harisovcina/Air/3Ddesign/3dprintedparts.jpg

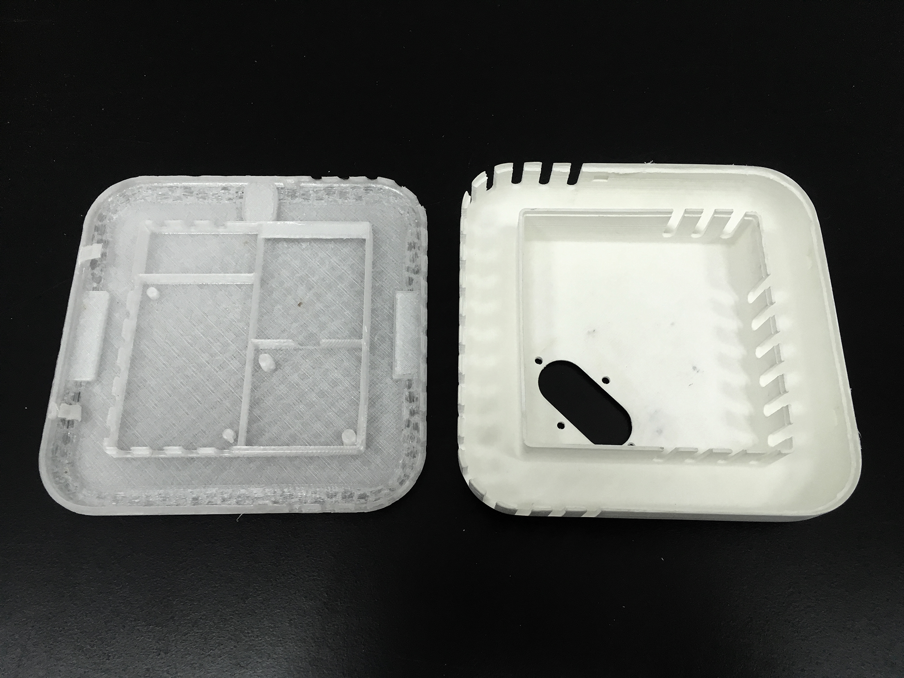
3Ddesign/3dprintedparts.jpg
