harisovcina/Air/3Ddesign/DSC_0951.jpg

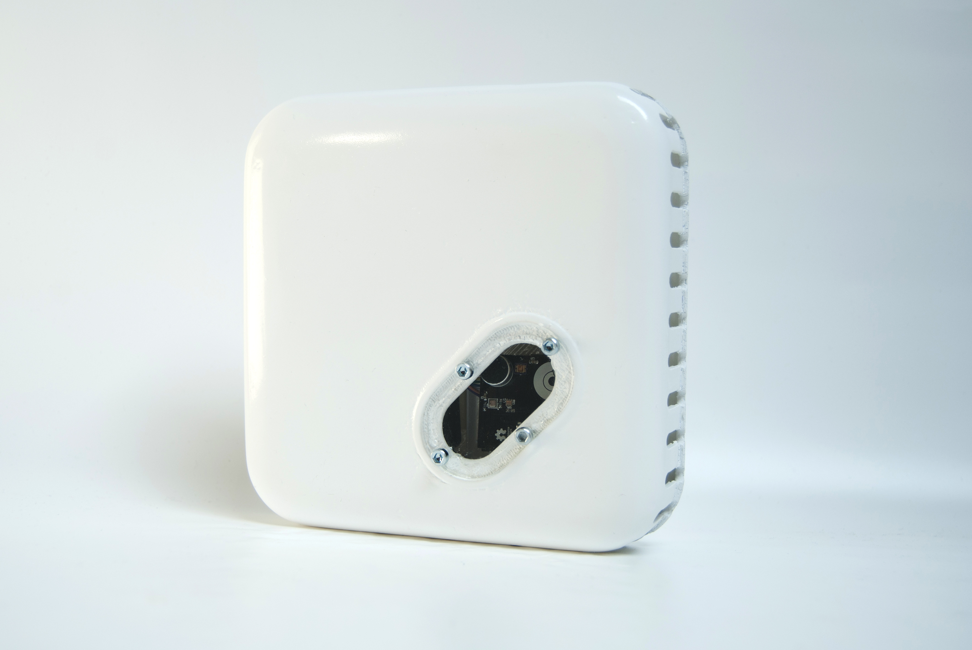
3Ddesign/DSC_0951.jpg
