harisovcina/Air/3Ddesign/DSC_0952.jpg

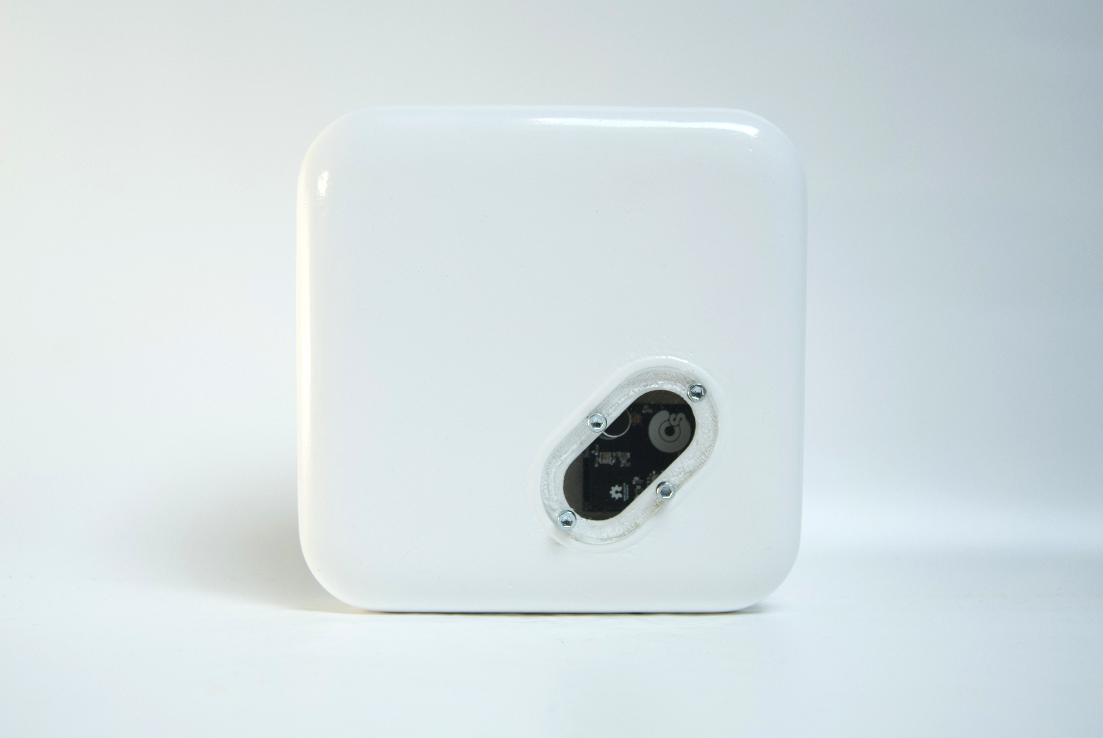
3Ddesign/DSC_0952.jpg
