harisovcina/Air/3Ddesign/Pasted image at 2016_08_31 05_55 PM.png

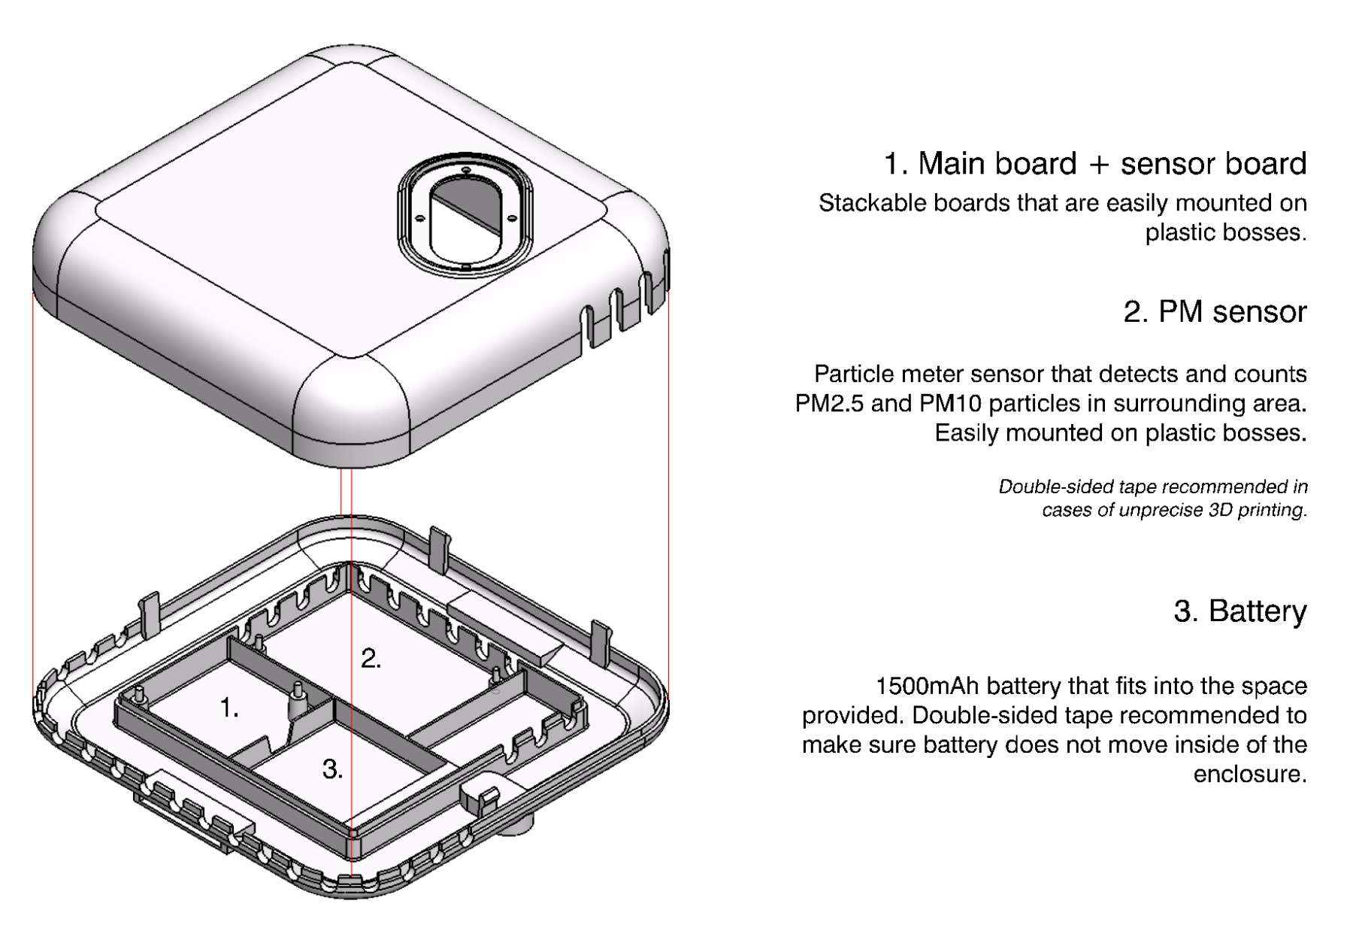
3Ddesign/Pasted image at 2016_08_31 05_55 PM.png
