harisovcina/Air/Hardware/Main Board/main board.jpg

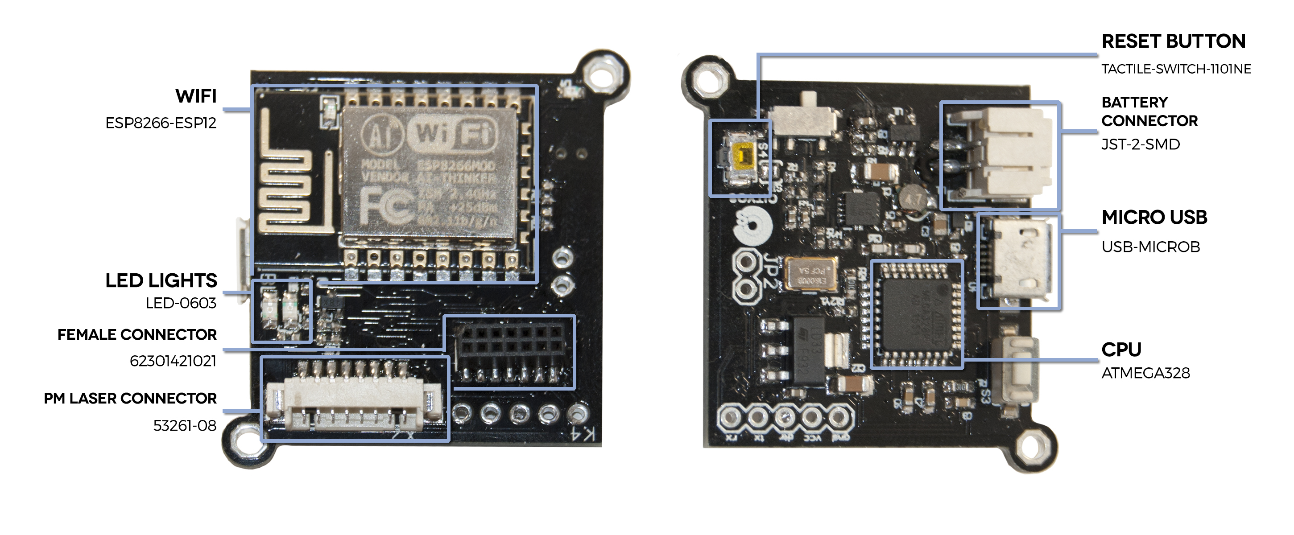
Hardware/Main Board/main board.jpg
