harisovcina/Air/Hardware/Wiki/CO-NO2-back.jpg

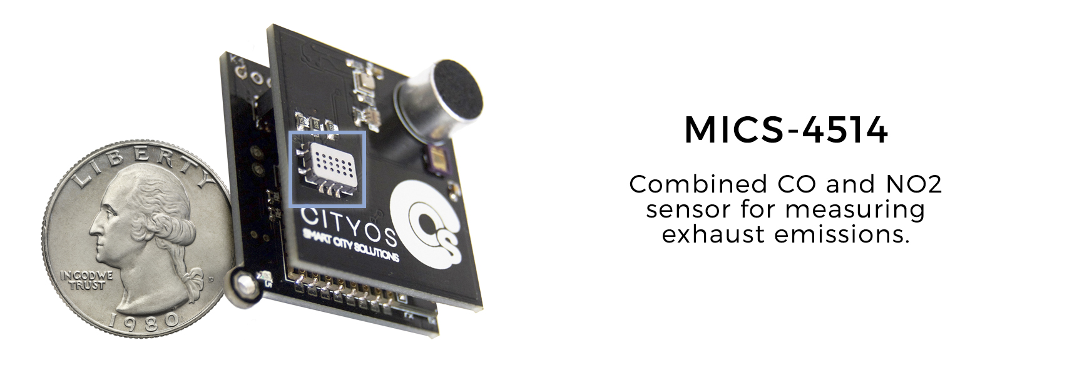
Hardware/Wiki/CO-NO2-back.jpg
