harisovcina/Air/Hardware/Wiki/connector_header.jpg

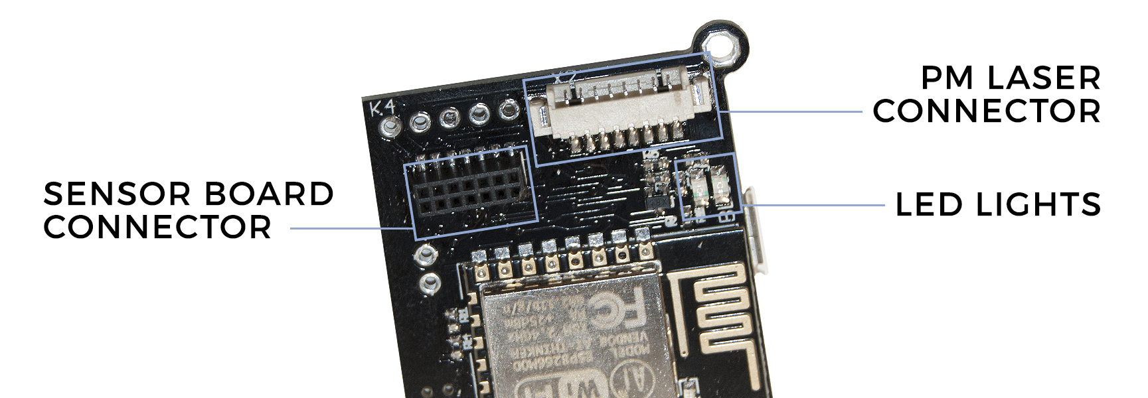
Hardware/Wiki/connector_header.jpg
