harisovcina/Air/Hardware/Wiki/Header-pic/mainboard_header.jpg

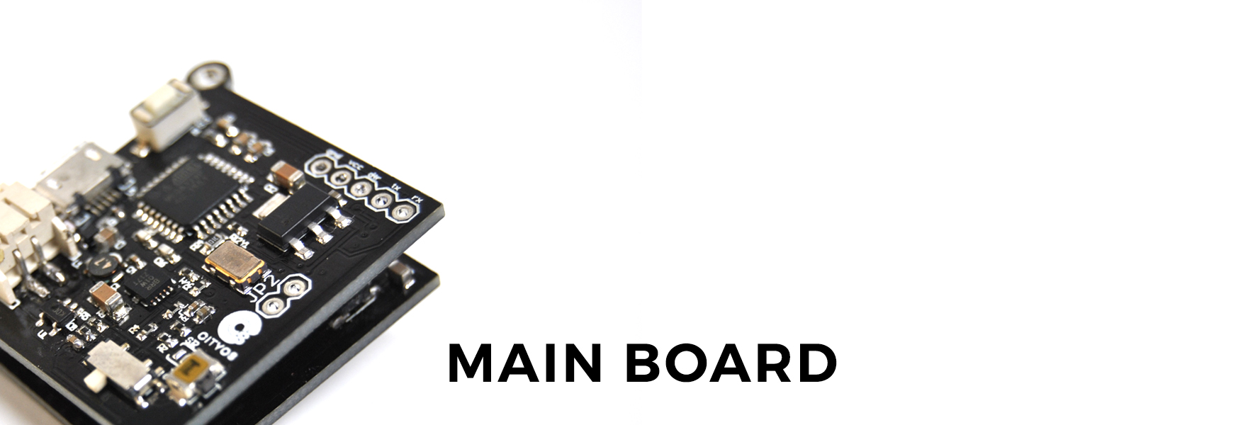
Hardware/Wiki/Header-pic/mainboard_header.jpg
