harisovcina/Air/Hardware/Wiki/Light_back.jpg

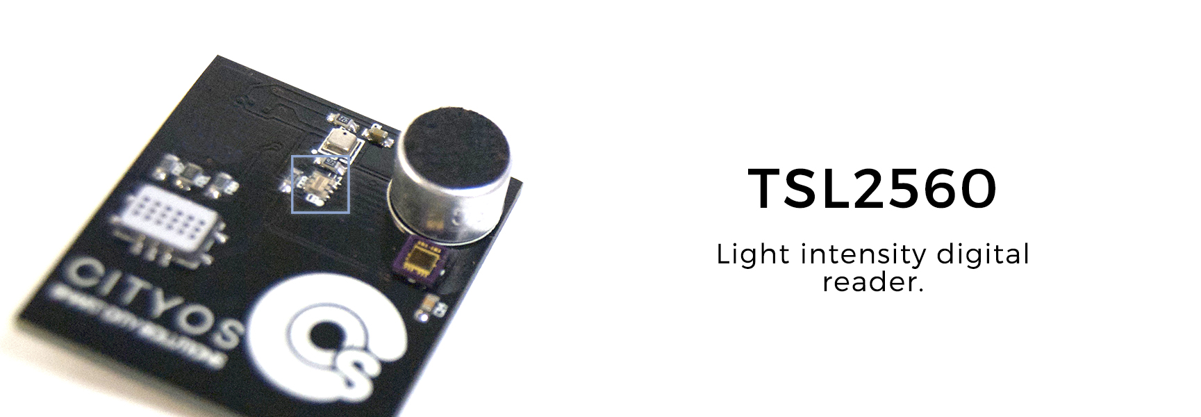
Hardware/Wiki/Light_back.jpg
