harisovcina/Air/Hardware/Wiki/LIPO834250.png

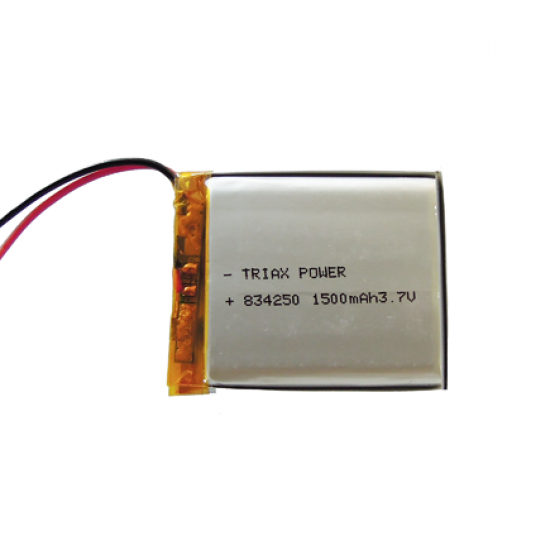
Hardware/Wiki/LIPO834250.png
