harisovcina/Air/Hardware/Wiki/Mic_UV_back.jpg

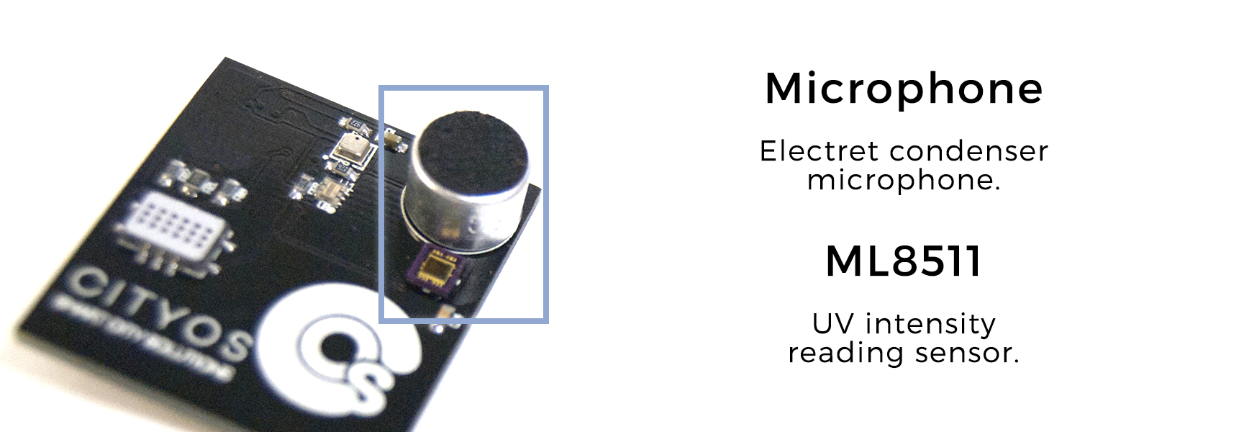
Hardware/Wiki/Mic_UV_back.jpg
